djtersteegc/rx02-emulator-mega-shield/Board v1.0.PNG

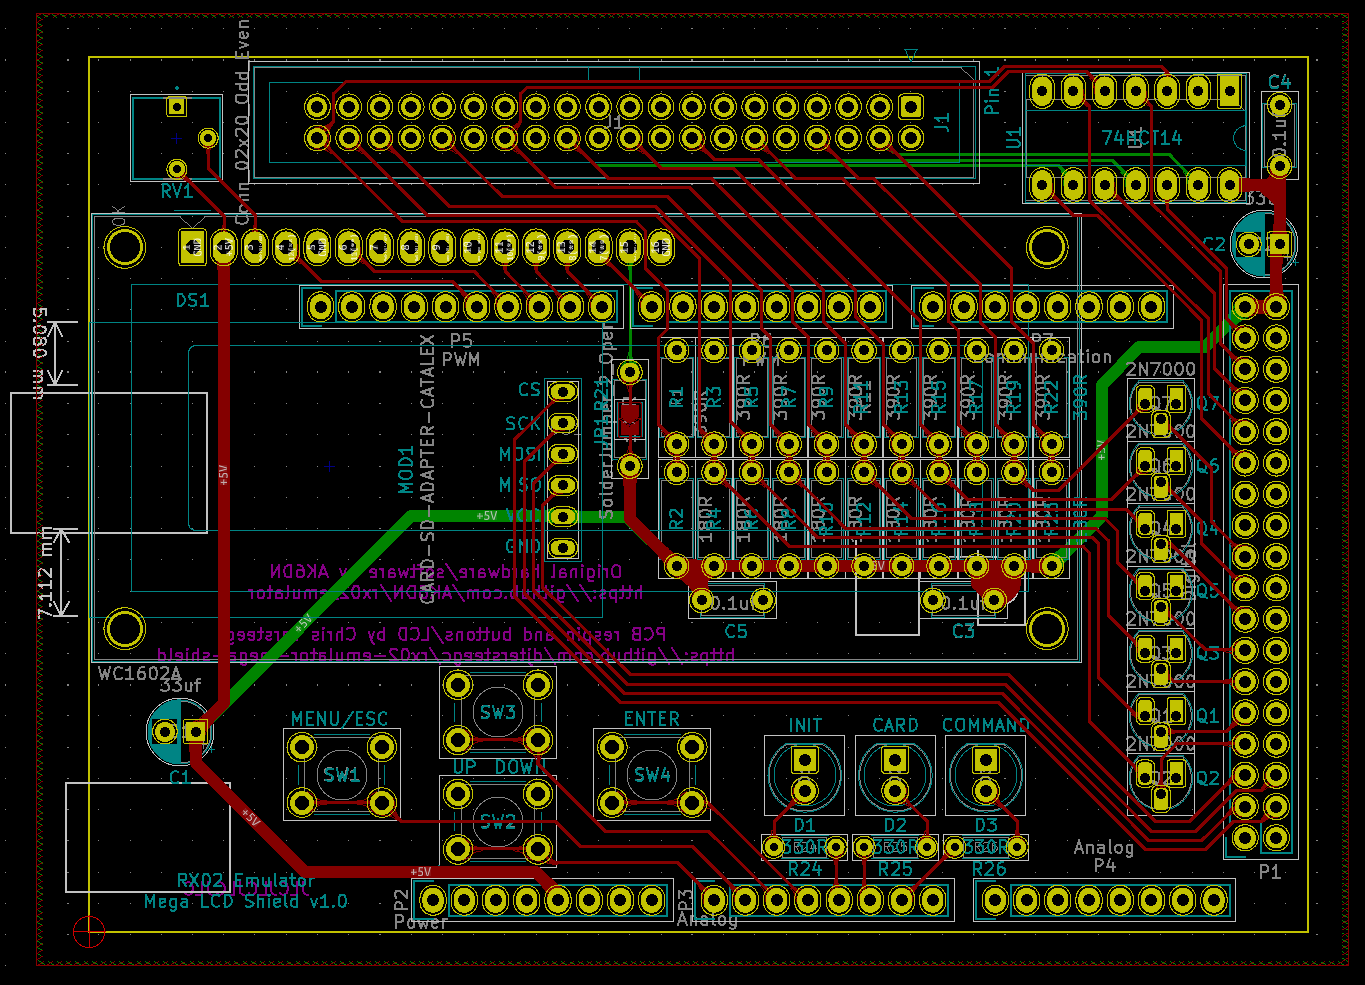
Board v1.0.PNG
